armpitMFG/OSSM-Parts/Model Assets/Reference Board/Cutout Template.png

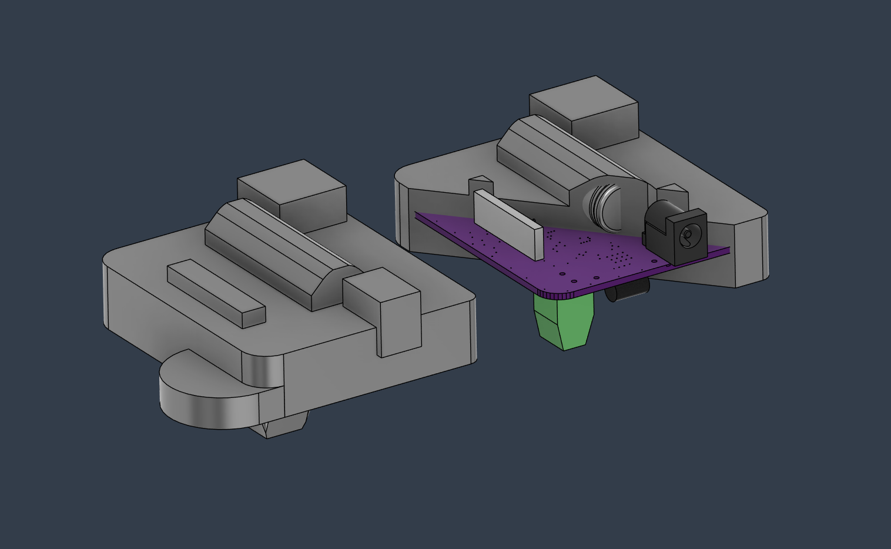
Model Assets/Reference Board/Cutout Template.png
