armpitMFG/OSSM-Parts/OSSM Tools/just_b Wrench/Images/Render.png

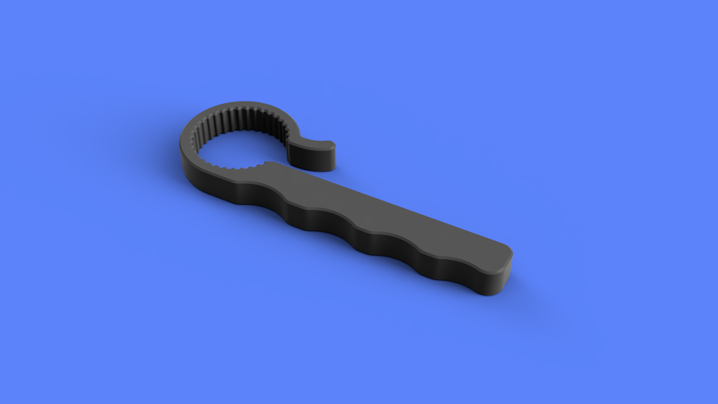
OSSM Tools/just_b Wrench/Images/Render.png
