armpitMFG/OSSM-Parts/OSSM v2 AIO PCB Backpack Mod/Files/Faceplates/Preview - Keep Calm And OSSM On.png

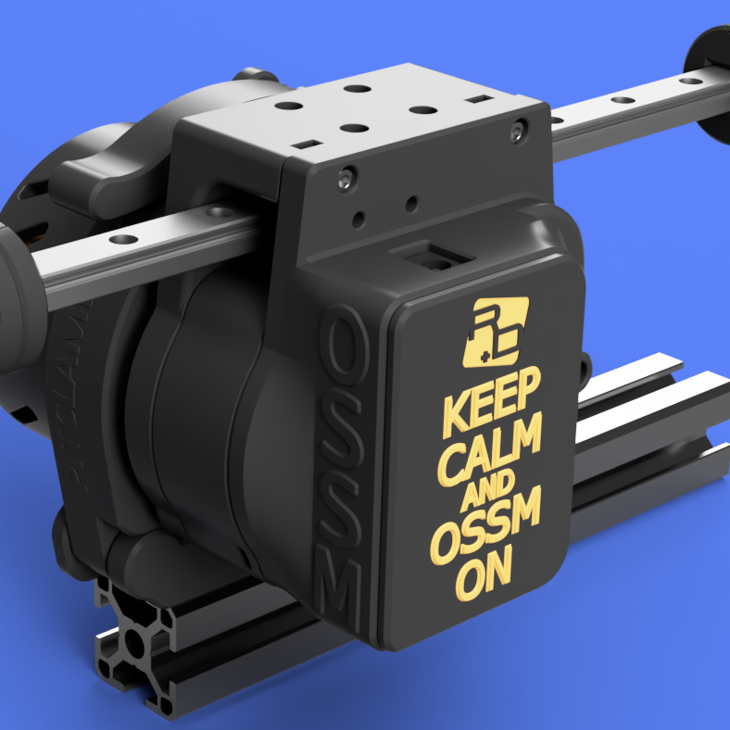
OSSM v2 AIO PCB Backpack Mod/Files/Faceplates/Preview - Keep Calm And OSSM On.png
