armpitMFG/OSSM-Parts/Remote Knobs/STEP/Remote Knob - Simple.step

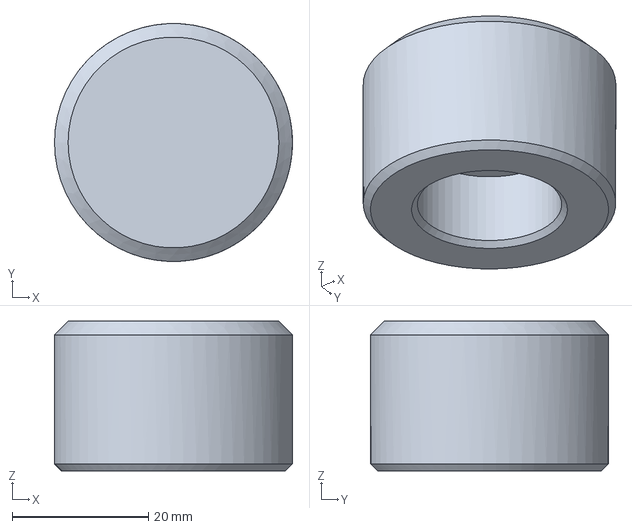
[picture p46: CAD file, 2024-08-20]
Remote Knobs/STEP/Remote Knob - Simple.step
35.0 x 35.0 x 22.0 mm
