armpitMFG/OSSM-Parts/Remote Reimagined/Files/OSSM - Remote Reimagined.3mf

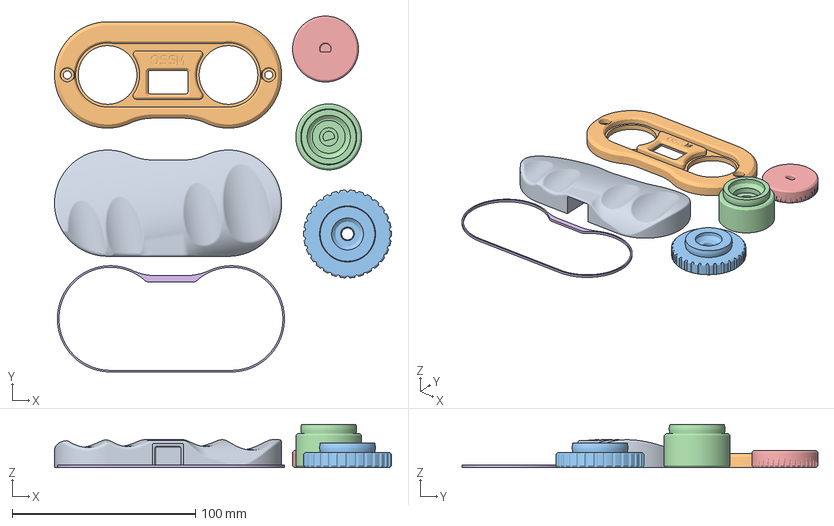
[picture p47: CAD file, 2024-09-08]
Remote Reimagined/Files/OSSM - Remote Reimagined.3mf
184.0 x 194.3 x 23.5 mm
OSSM - Remote Reimagined - Bottom - Ergo.step
OSSM - Remote Reimagined - Board Interface.step
OSSM - Remote Reimagined - Speed Knob Helper.step
OSSM - Remote Reimagined - Speed Knob.step
OSSM - Remote Reimagined - Depth Knob.step
OSSM - Remote Reimagined - Accent Stripe.step
