armpitMFG/OSSM-Parts/Remote Reimagined/Files/STEP/OSSM - Remote Reimagined - Board Interface V1.1.step

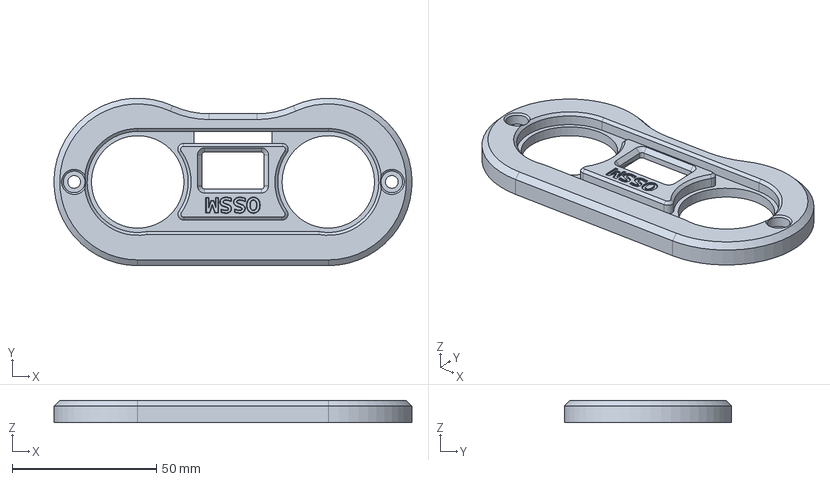
[picture p48: CAD file, 2025-01-22]
Remote Reimagined/Files/STEP/OSSM - Remote Reimagined - Board Interface V1.1.step
124.0 x 57.9 x 7.70 mm
