armpitMFG/OSSM-Parts/Toy Mounts/OSSM Tie Down And Suction Plate 110mm/Files/Preconfigured 3mf Files/OSSM Tie Down And Suction Plate 110mm (Smooth PEI).3mf

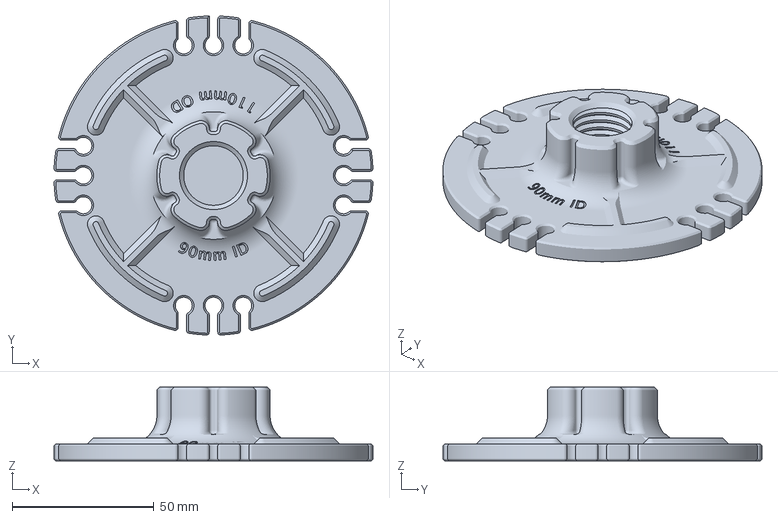
[picture p49: CAD file, 2025-02-27]
Toy Mounts/OSSM Tie Down And Suction Plate 110mm/Files/Preconfigured 3mf Files/OSSM Tie Down And Suction Plate 110mm (Smooth PEI).3mf
112.6 x 112.6 x 26.0 mm
