armpitMFG/OSSM-Parts/Metal Hinge Printed Files/STEP/Hinge Lever Bushing.step

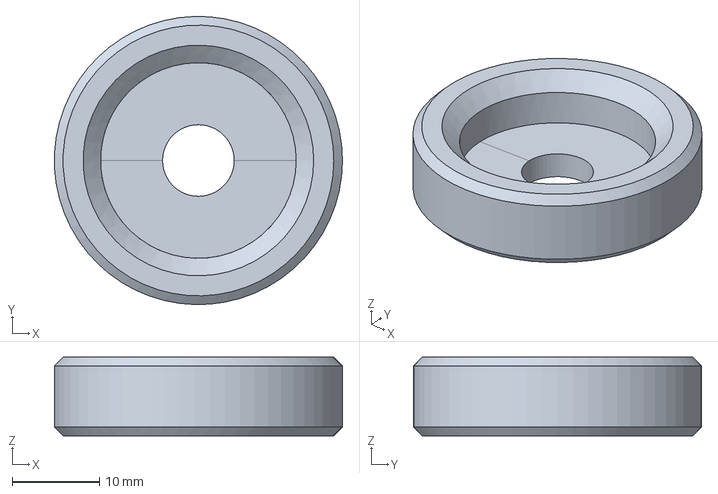
[picture p50: CAD file, 2024-08-17]
Metal Hinge Printed Files/STEP/Hinge Lever Bushing.step
33.0 x 33.0 x 9.00 mm
