armpitMFG/OSSM-Parts/Model Assets/Misc/INIU P63-E1 BETA.STEP

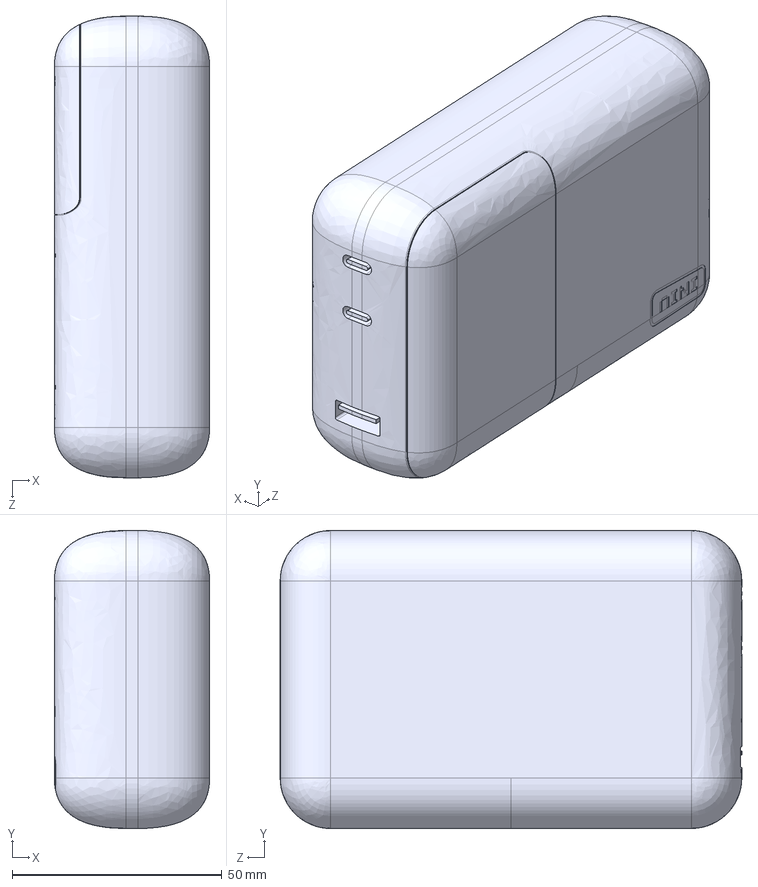
[picture p51: CAD file, 2024-10-24]
Model Assets/Misc/INIU P63-E1 BETA.STEP
37.0 x 71.0 x 110.0 mm
