armpitMFG/OSSM-Parts/Model Assets/Motors/42AIM30.step

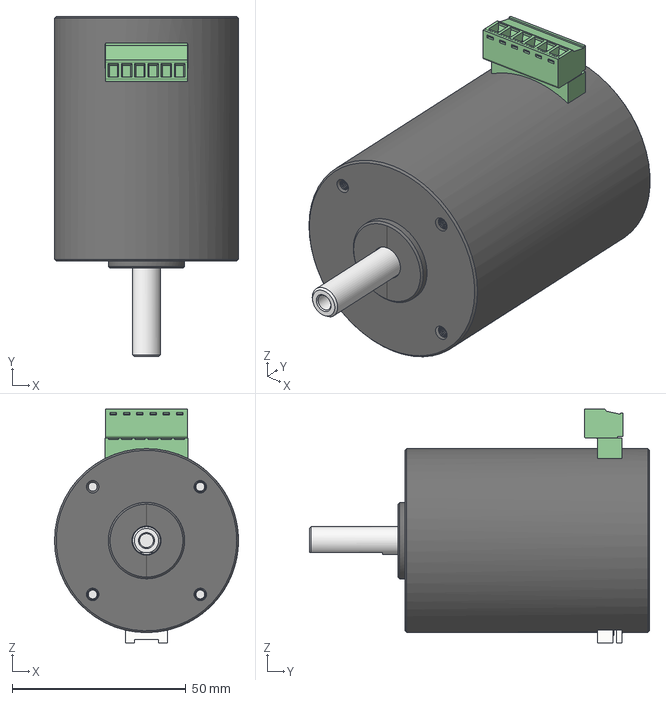
[picture p52: CAD file, 2024-08-19]
Model Assets/Motors/42AIM30.step
53.0 x 98.0 x 67.4 mm
