armpitMFG/OSSM-Parts/OSSM Reference PCB Housing With Strain Relief/Release Files/STEP/OSSM_Reference_PCB_Housing_V2_StrainRelief_Bottom_Reinforced_Widened_RC1.step

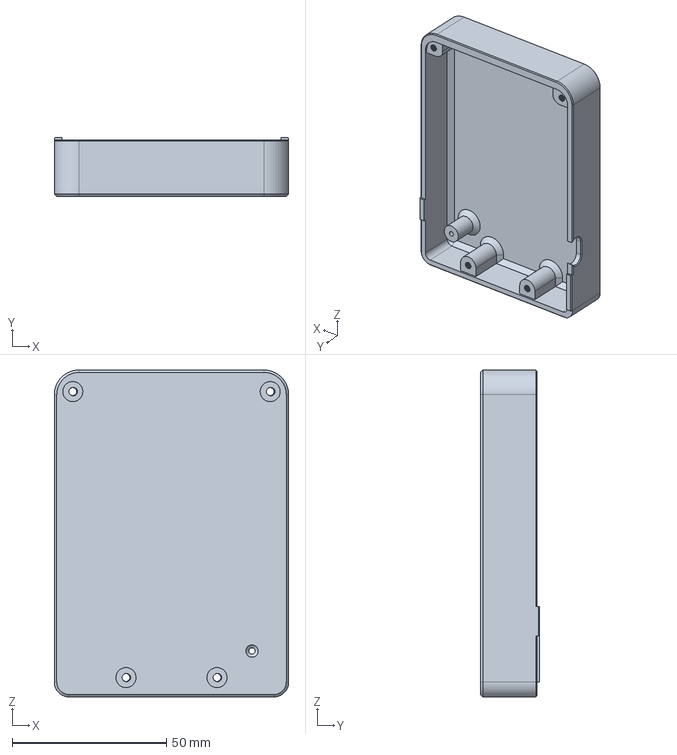
[picture p54: CAD file, 2024-12-05]
OSSM Reference PCB Housing With Strain Relief/Release Files/STEP/OSSM_Reference_PCB_Housing_V2_StrainRelief_Bottom_Reinforced_Widened_RC1.step
76.0 x 19.2 x 106.0 mm
