armpitMFG/OSSM-Parts/OSSM v2 AIO PCB Backpack Mod/Files/Faceplates/RD OSSM.stl

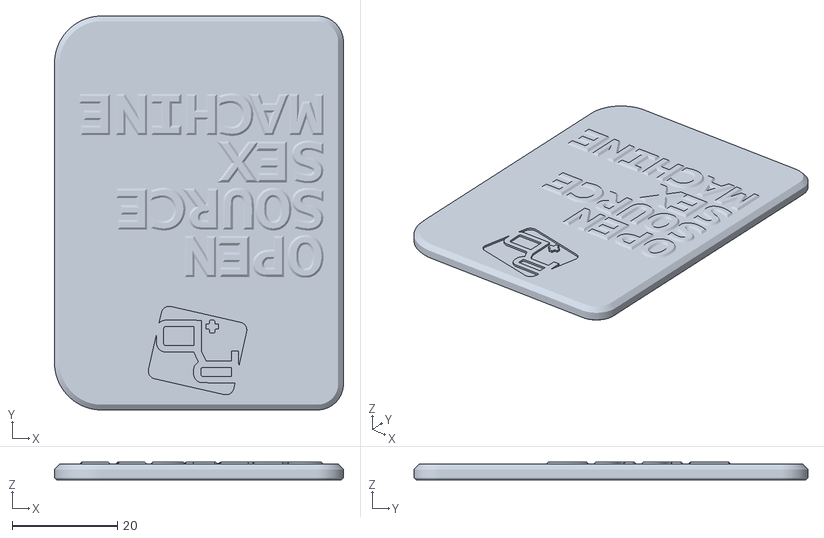
[picture p55: CAD file, 2025-05-14]
OSSM v2 AIO PCB Backpack Mod/Files/Faceplates/RD OSSM.stl
55.0 x 75.0 x 3.40
