armpitMFG/OSSM-Parts/OSSM v2 AIO PCB Backpack Mod/Files/Preconfigured 3mf Files/[BBL_P1S] OSSM v2 AIO PCB Backpack Mod.3mf

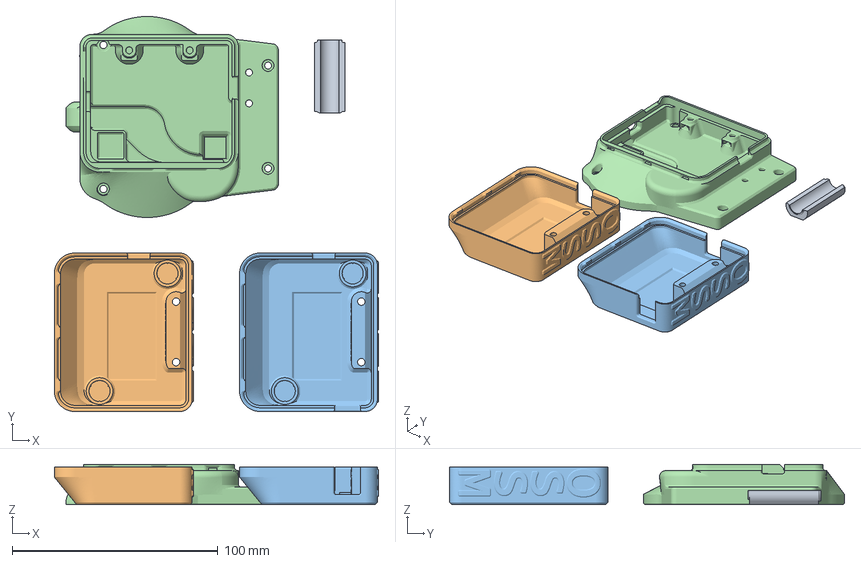
[picture p56: CAD file, 2025-08-20]
OSSM v2 AIO PCB Backpack Mod/Files/Preconfigured 3mf Files/[BBL_P1S] OSSM v2 AIO PCB Backpack Mod.3mf
157.6 x 191.9 x 19.5 mm
Wire Cover
OSSM Mods - AIO PCB Backpack - Cap (No RJ45).stp
OSSM Mods - AIO PCB Backpack - Cap (Default).stp
OSSM Mods - AIO PCB Backpack - Base.step
