armpitMFG/OSSM-Parts/OSSM v2 AIO PCB Backpack Mod/Files/STEP/OSSM Mods - AIO PCB Backpack - Wire Cover.stp

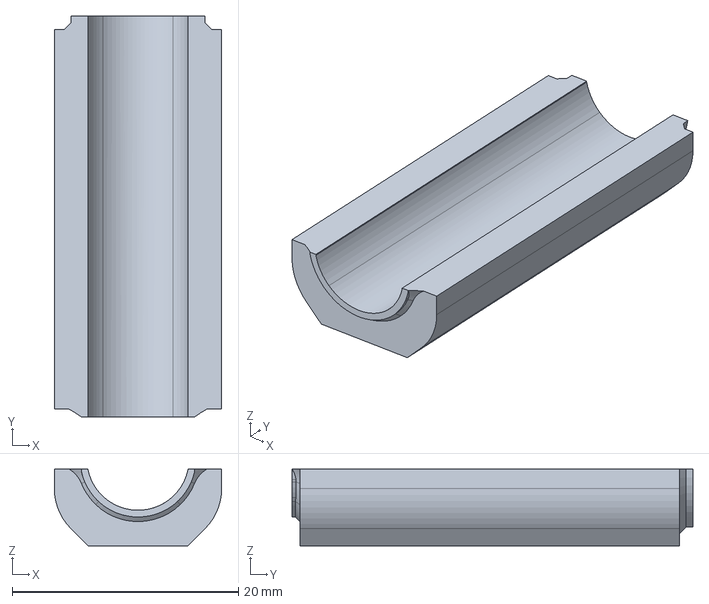
[picture p57: CAD file, 2025-08-20]
OSSM v2 AIO PCB Backpack Mod/Files/STEP/OSSM Mods - AIO PCB Backpack - Wire Cover.stp
14.8 x 35.5 x 6.80 mm
