armpitMFG/OSSM-Parts/OSSM v2 AIO PCB Backpack Mod/Files/Strain Relief/OSSM Mods - AIO PCB Backpack - Strain Relief - Adafruit 20v USBC 90 Degree.stl

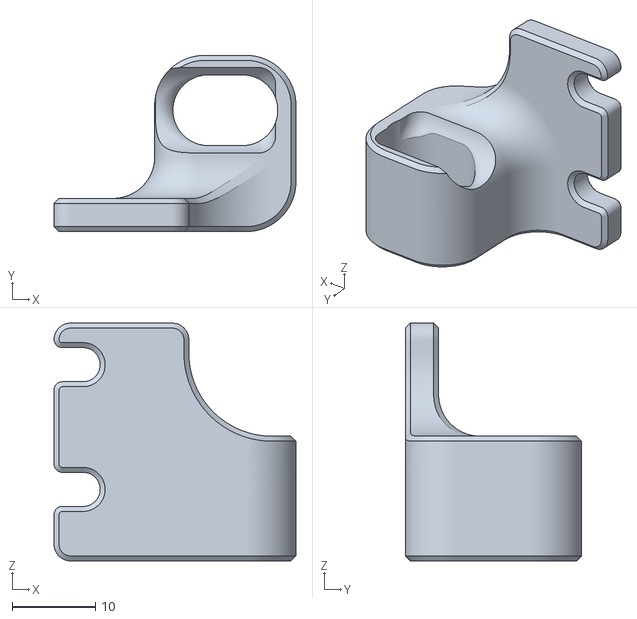
[picture p58: CAD file, 2024-12-23]
OSSM v2 AIO PCB Backpack Mod/Files/Strain Relief/OSSM Mods - AIO PCB Backpack - Strain Relief - Adafruit 20v USBC 90 Degree.stl
29.1 x 21.2 x 28.6
