armpitMFG/OSSM-Parts/OSSM v2 AIO PCB Backpack Mod/Files/Strain Relief/STEP/OSSM Mods - AIO PCB Backpack - Strain Relief - uxcell 90 Degree 5.5x2.step

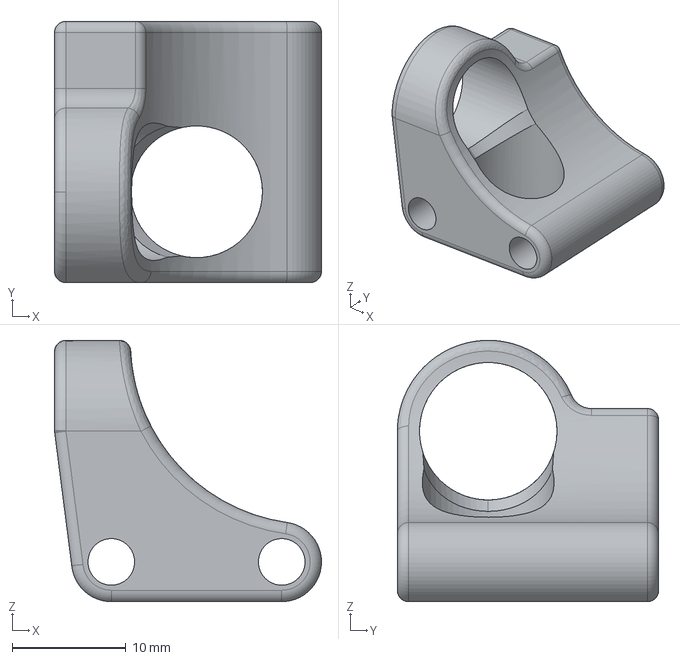
[picture p59: CAD file, 2026-01-03]
OSSM v2 AIO PCB Backpack Mod/Files/Strain Relief/STEP/OSSM Mods - AIO PCB Backpack - Strain Relief - uxcell 90 Degree 5.5x2.step
23.5 x 23.0 x 23.0 mm
