armpitMFG/OSSM-Parts/Remote Knobs/STEP/Remote Knob - Knurled With Position Indicator.step

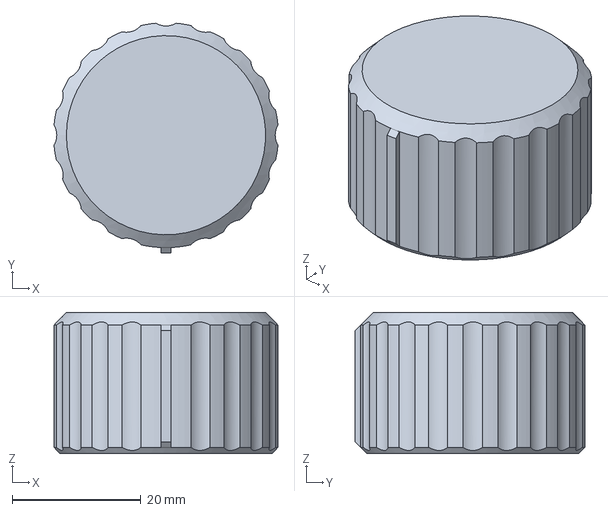
[picture p60: CAD file, 2024-08-20]
Remote Knobs/STEP/Remote Knob - Knurled With Position Indicator.step
34.9 x 35.7 x 22.0 mm
