armpitMFG/OSSM-Parts/Remote Reimagined/Files/STEP/OSSM - Remote Reimagined - Speed Knob Helper.step

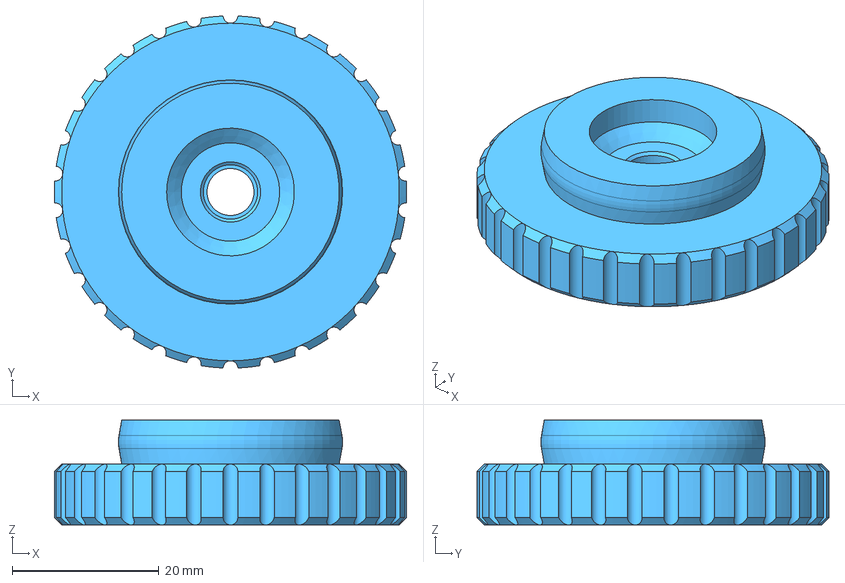
[picture p61: CAD file, 2024-09-09]
Remote Reimagined/Files/STEP/OSSM - Remote Reimagined - Speed Knob Helper.step
48.0 x 48.0 x 14.3 mm
