armpitMFG/OSSM-Parts/Metal Hinge Printed Files/STEP/Hinge Plate Knob M8 For Metal.step

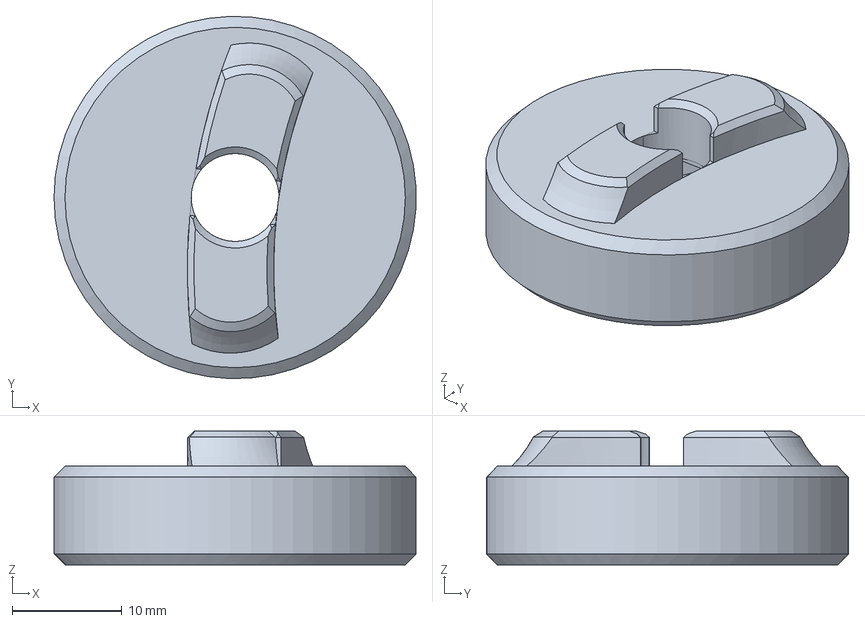
[picture p62: CAD file, 2024-08-17]
Metal Hinge Printed Files/STEP/Hinge Plate Knob M8 For Metal.step
33.0 x 33.0 x 12.2 mm
