armpitMFG/OSSM-Parts/Model Assets/Motors/57AIM30.step

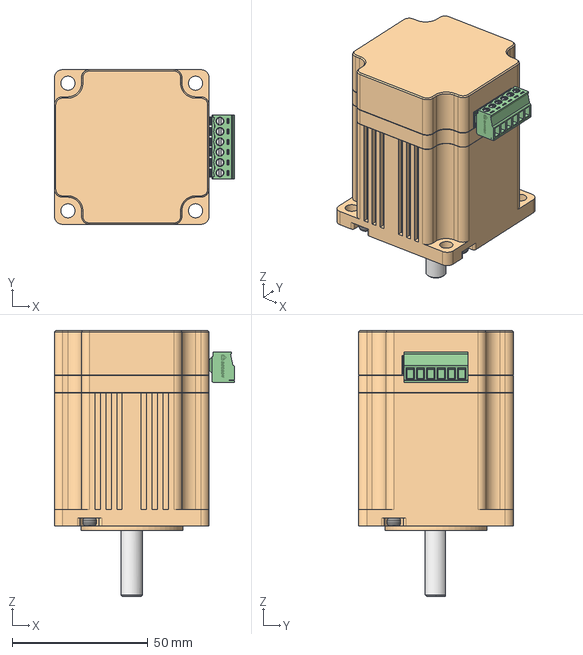
[picture p63: CAD file, 2024-08-19]
Model Assets/Motors/57AIM30.step
66.4 x 57.0 x 98.0 mm
