armpitMFG/OSSM-Parts/OSSM Motor Cover/Files/STEP/PitClamp Mini - Motor Cover - 57AIM30 - Rear - Sealed.step

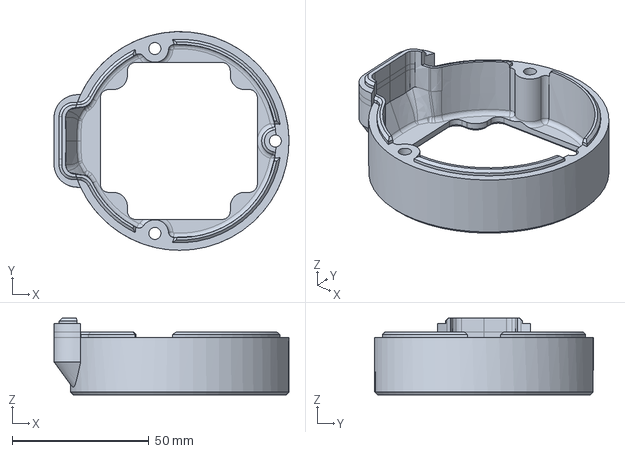
[picture p64: CAD file, 2024-09-30]
OSSM Motor Cover/Files/STEP/PitClamp Mini - Motor Cover - 57AIM30 - Rear - Sealed.step
85.9 x 80.0 x 28.0 mm
