armpitMFG/OSSM-Parts/OSSM v2 AIO PCB Backpack Mod/Files/STEP/OSSM Mods - AIO PCB Backpack - Base V2.3c.stp

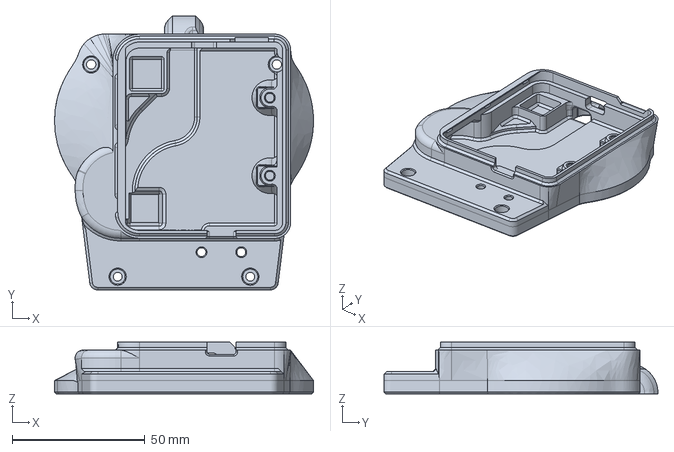
[picture p65: CAD file, 2025-07-16]
OSSM v2 AIO PCB Backpack Mod/Files/STEP/OSSM Mods - AIO PCB Backpack - Base V2.3c.stp
97.7 x 103.3 x 19.5 mm
