armpitMFG/OSSM-Parts/Remote Reimagined/Files/STEP/OSSM - Remote Reimagined - Speed Knob.step

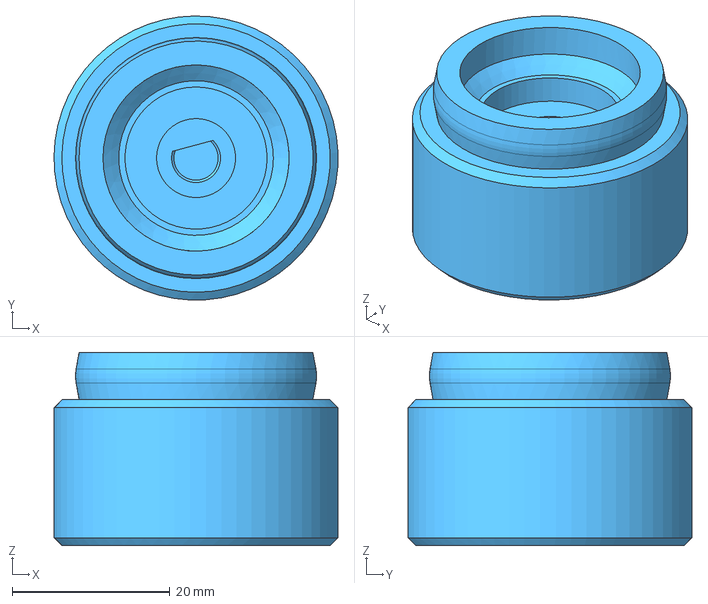
[picture p66: CAD file, 2024-09-09]
Remote Reimagined/Files/STEP/OSSM - Remote Reimagined - Speed Knob.step
36.0 x 36.0 x 24.5 mm
