armpitMFG/OSSM-Parts/OSSM Motor Cover/Files/STEP/PitClamp Mini - Motor Cover - 57AIM30 - Ring Interface - Vented.step

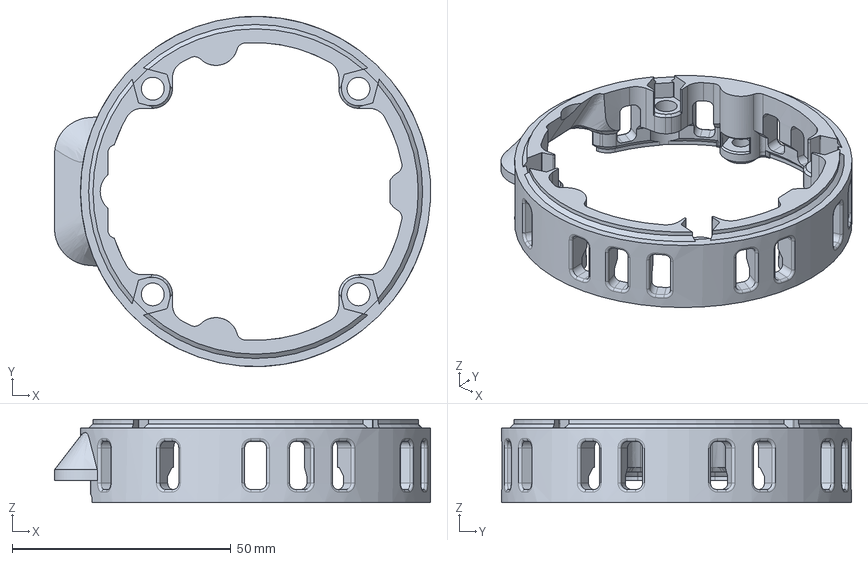
[picture p67: CAD file, 2024-09-30]
OSSM Motor Cover/Files/STEP/PitClamp Mini - Motor Cover - 57AIM30 - Ring Interface - Vented.step
85.9 x 80.0 x 19.0 mm
