armpitMFG/OSSM-Parts/OSSM v2 AIO PCB Backpack Mod/Files/Faceplates/OSSM v2 AIO PCB Backpack - Faceplate Template.step

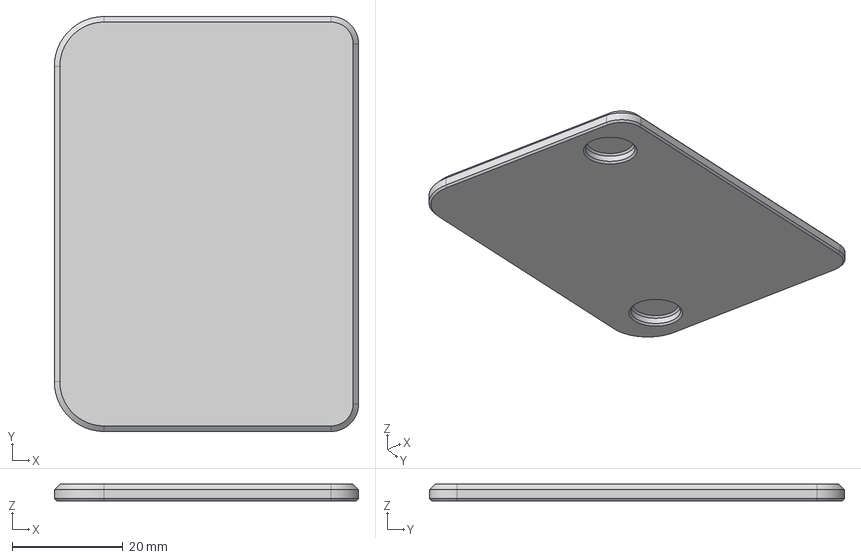
[picture p68: CAD file, 2024-12-21]
OSSM v2 AIO PCB Backpack Mod/Files/Faceplates/OSSM v2 AIO PCB Backpack - Faceplate Template.step
55.0 x 75.0 x 3.00 mm
