armpitMFG/OSSM-Parts/OSSM v2 AIO PCB Backpack Mod/Files/STEP/OSSM Mods - AIO PCB Backpack - Cap (Default).stp

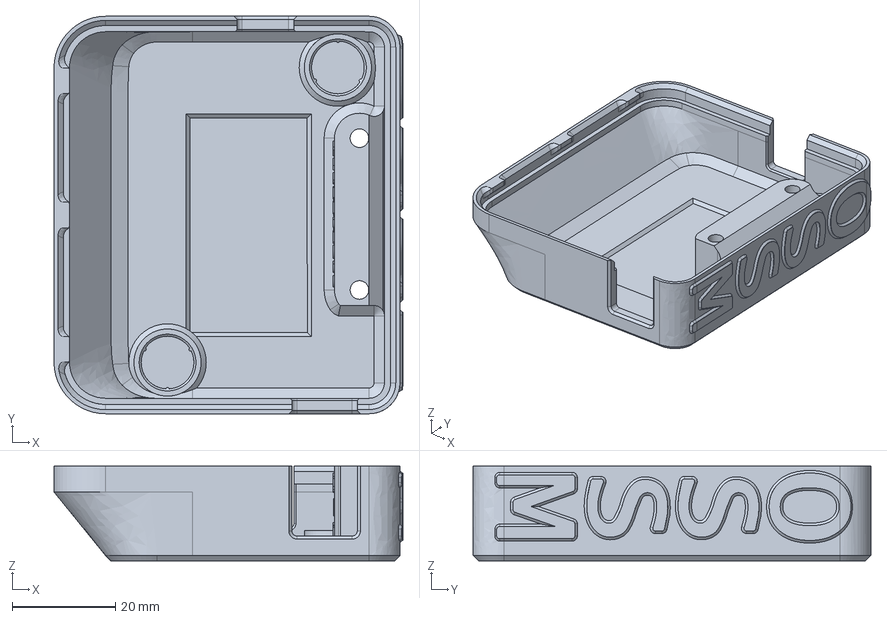
[picture p69: CAD file, 2025-04-13]
OSSM v2 AIO PCB Backpack Mod/Files/STEP/OSSM Mods - AIO PCB Backpack - Cap (Default).stp
67.6 x 77.0 x 18.3 mm
