armpitMFG/OSSM-Parts/OSSM v2 AIO PCB Backpack Mod/Files/Strain Relief/STEP/OSSM v2 AIO PCB Backpack - Strain Relief Template.step

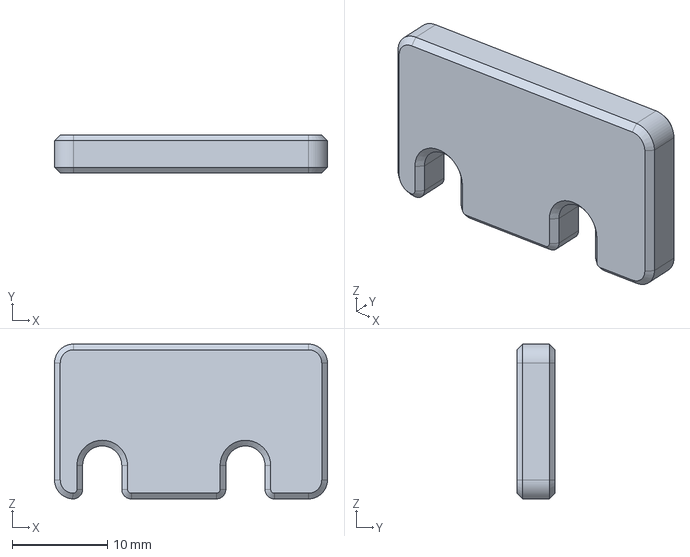
[picture p70: CAD file, 2024-12-23]
OSSM v2 AIO PCB Backpack Mod/Files/Strain Relief/STEP/OSSM v2 AIO PCB Backpack - Strain Relief Template.step
28.6 x 4.00 x 16.2 mm
