armpitMFG/OSSM-Parts/Remote Reimagined/Files/STEP/OSSM - Remote Reimagined - Accent Stripe.step

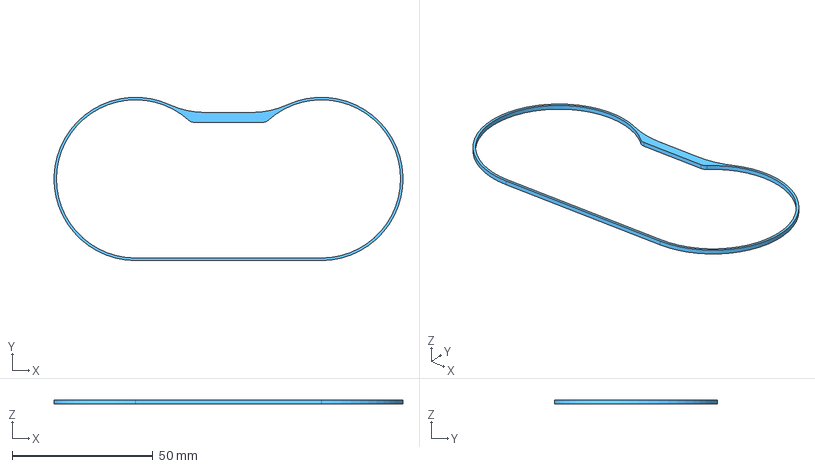
[picture p71: CAD file, 2024-09-08]
Remote Reimagined/Files/STEP/OSSM - Remote Reimagined - Accent Stripe.step
124.0 x 57.9 x 1.50 mm
