armpitMFG/OSSM-Parts/OSSM v2 AIO PCB Backpack Mod/Files/Faceplates/Keep Calm And OSSM On.step

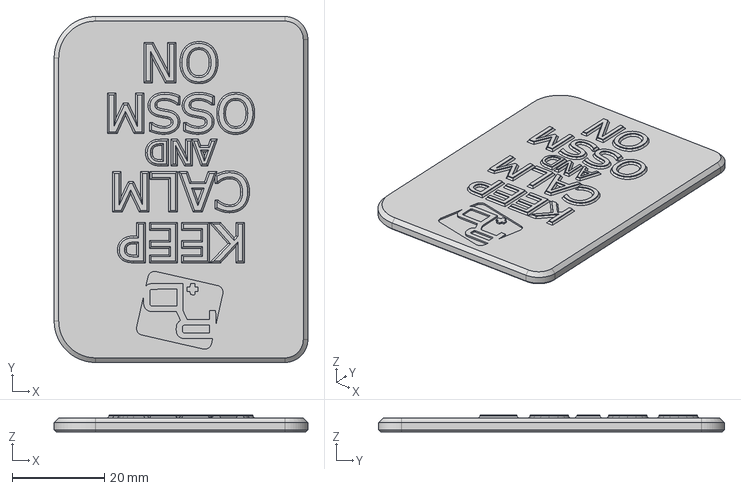
[picture p72: CAD file, 2024-12-21]
OSSM v2 AIO PCB Backpack Mod/Files/Faceplates/Keep Calm And OSSM On.step
55.0 x 75.0 x 3.60 mm
