armpitMFG/OSSM-Parts/Remote Reimagined/Files/STEP/OSSM - Remote Reimagined - Bottom - Ergo.step

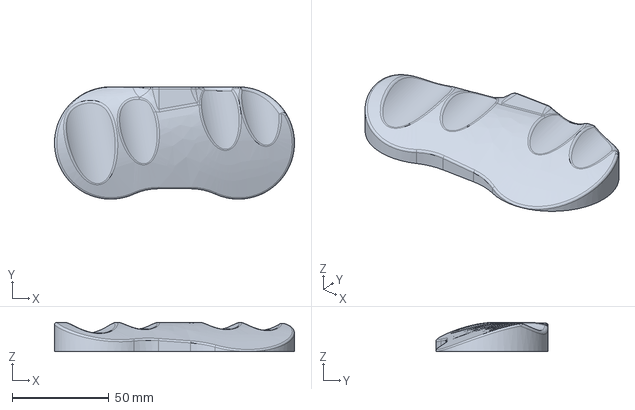
[picture p73: CAD file, 2024-09-08]
Remote Reimagined/Files/STEP/OSSM - Remote Reimagined - Bottom - Ergo.step
124.0 x 58.0 x 15.2 mm
