armpitMFG/OSSM-Parts/Remote Reimagined/Files/STEP/OSSM - Remote Reimagined - Depth Knob.step

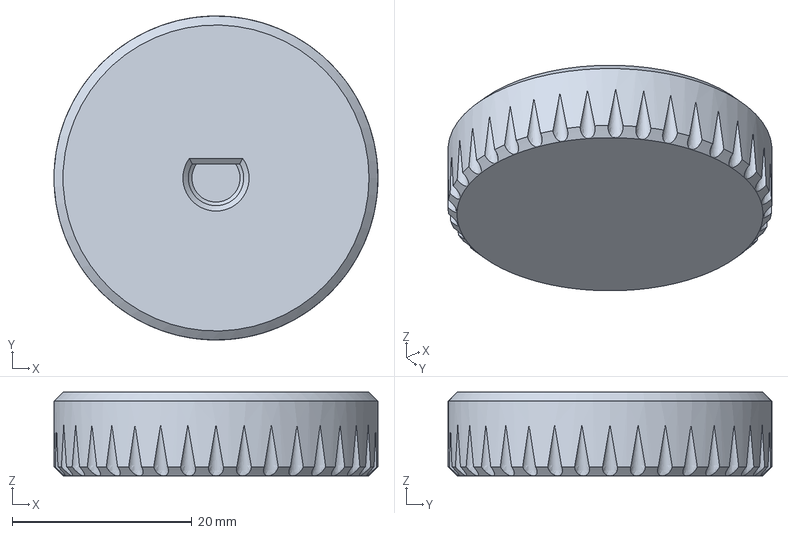
[picture p74: CAD file, 2024-09-08]
Remote Reimagined/Files/STEP/OSSM - Remote Reimagined - Depth Knob.step
36.0 x 36.0 x 9.30 mm
